JSkrat/kagami-house-black-debug/fw/1202_lib.c

#include "1202_lib.h"
#include <stdint.h>
#include <avr/pgmspace.h>
#include "KagamiCore/defines.h"
#include <util/delay.h>
#include "messages.h"
//#include "main.h"

//#define LCD_HUGE_FONT
//#define LCD_CYRILLIC_FONT
#define charDataWidth ((uint8_t) 5)
#define charWidth ((uint8_t) 6)
#define bigCharDataWidth ((uint8_t) 20)
#define bigCharWidth ((uint8_t) 12)

#ifdef USE_LCD

uint8_t lcdMutex = 0;
uint8_t lcd_x, lcd_y;

const uint8_t font_1[] PROGMEM = {
    0b00001110, 0b01011111, 0b00001110, 0b00000000, 0b00000000, // !
    0b00000110, 0b00001110, 0b00000000, 0b00001110, 0b00000110, // "
    0b00100100, 0b01111110, 0b00100100, 0b01111110, 0b00100100, // #
    0b00100100, 0b00101010, 0b01111111, 0b00101010, 0b00010010, // $
    0b01000100, 0b00100100, 0b00010000, 0b01001000, 0b01000100, // %
    0b00110100, 0b01001010, 0b01011010, 0b00100100, 0b01010000, // &
    0b00001000, 0b00000110, 0b00000000, 0b00000000, 0b00000000, // '
    0b00000000, 0b00000000, 0b00000000, 0b00111110, 0b01000001, // (
    0b01000001, 0b00111110, 0b00000000, 0b00000000, 0b00000000, // )
    0b00001010, 0b00000100, 0b00011111, 0b00000100, 0b00001010, // *
    0b00010000, 0b00010000, 0b01111100, 0b00010000, 0b00010000, // +
    0b10000000, 0b01000000, 0b00000000, 0b00000000, 0b00000000, // ,
    0b00010000, 0b00010000, 0b00010000, 0b00010000, 0b00010000, // -
    0b00000000, 0b01000000, 0b01000000, 0b00000000, 0b00000000, // .
    0b01000000, 0b00100000, 0b00010000, 0b00001000, 0b00000100, // /
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
    // display rotate :)
    LCD_write_byte(0xA0, 0); // segment driver direction select (column inversion, A0/A1)
    LCD_write_byte(0xC0, 0); // common driver direction select (line inversion, C0/C8)
    lcd_x = 0; lcd_y = 0;
    lcdMutex = 0;
}

void lcdLocate(uint8_t y, uint8_t x) { // 471 clocks (59us)
    if (lcdMutex) return;
    lcdMutex = 1;
    y &= 0x0F;
    x = (x & 0x0F) * FONT_WIDTH;
    lcd_x = x; lcd_y = y;
    LCD_write_byte(0xB0 | y, 0); // set page address (row)
    LCD_write_byte(x & 0x0F, 0); // set column address lower nibble
    LCD_write_byte(0x10 | ((x >> 4) & 0x07), 0); // set column address higher nibble
    lcdMutex = 0;
}

void lcdGotoXY(uint8_t x, uint8_t y) { // 464 clocks (58us)
    if (lcdMutex) return;
    lcdMutex = 1;
    y &= 0x0F;
    lcd_x = x & 0x7F; lcd_y = y;
    LCD_write_byte(0xB0 | y, 0); // set page address (row)
    LCD_write_byte(x & 0x0F, 0); // set column address lower nibble
    LCD_write_byte(0x10 | ((x >> 4) & 0x07), 0); // set column address higher nibble
    lcdMutex = 0;
}

void lcdPrintChar(uint8_t symbol, tFontStyle style) { // 947 clocks (118us)+
    const uint8_t *start;
    if (! (style & huge)) {
        start = &font_1[0];
#ifdef LCD_CYRILLIC_FONT
        if (symbol >= 0xE0) {
            start = (&font_3[0]) + ((uint16_t) symbol - 0xE0) * charDataWidth;
        } else if (symbol >= 0xA0) {
            start = (&font_2[0]) + ((uint16_t) symbol - 0xA0) * charDataWidth;
        } else if (symbol >= 0x20) {
#else
		if (symbol < 0xA0 && symbol >= 0x20) {
#endif
            start = (&font_1[0]) + ((uint16_t) symbol - 0x21) * charDataWidth;
        } else return;
    } else {
#ifdef LCD_HUGE_FONT
        if ((symbol < '0' || symbol > '9') && symbol != ' ') return;
        start = &big_digits_lcd12x16[0] + (symbol - '0') * bigCharDataWidth;
#else
		return;
#endif
    }

    int8_t offset = 0-1;
    for (int8_t i = 0; i < ((style & huge)? bigCharWidth*2: charWidth); i++) {
        uint8_t col;
        if ((style & huge) && i == bigCharWidth) {
            lcdGotoXY(lcd_x, lcd_y+1);
        }
        if ((style & huge) && (i == bigCharDataWidth/2 || i == bigCharDataWidth/2+1)) { // interletter spacing at first row
            col = 0;
        } else if (i < ((style & huge)? bigCharDataWidth+2: charDataWidth) && symbol != ' ') { // hardcoded space
            offset++;
            col = pgm_read_byte(&start[offset]);
        } else { // interletter spacing
            col = 0;
        }
        if (style & invisible) col = 0;
        if (style & inversed) col = ~col;
        LCD_write_byte(col, 1);
    }
    if (style & huge)
        lcdGotoXY(lcd_x+bigCharWidth, lcd_y-1);
    else
        lcd_x += charWidth;
}

#define META_PRINT(get_byte_func, message, style) \
    /*unsigned char symbol;*/ \
    int8_t count = 0; \
	int8_t length = get_byte_func; \
    do { \
	    message++; \
	    lcdPrintChar(get_byte_func, style); \
    } while (0 < length-- && LCD_COLUMNS > count++); \
    return count;


uint8_t lcdPrint(const string *message, tFontStyle style) { // 13 + (13 + lcdPrintChar) * length
	META_PRINT(pgm_read_byte(message), message, style);
}

uint8_t lcdRamPrint(const string *message, tFontStyle style) {
	META_PRINT((message->length), message, style);
}

void lcdClear() {
    lcdLocate(0, 0);
    for (uint16_t i = 0; i < ((uint16_t)LCD_WIDTH * LCD_PAGES); i++) {
        LCD_write_byte(0, 1);
    }
}

#endif // USE_LCD
